bm1810/DataLogger/SCRIPTS/Temperature Sensors/Temperature_Sensors/DigiTempResponse/DigiTempResponse.ino

/*
  Temperature Sensors
 This code will read the temperature from two temperature sensors:
   Dallas 18820
   TMP36
 */

#include <OneWire.h>
#include <DallasTemperature.h>

// Data wire is plugged into pin 3 on the Arduino
#define ONE_WIRE_BUS 3

// Setup a oneWire instance to communicate with any OneWire devices
OneWire oneWire(ONE_WIRE_BUS);

// Pass our oneWire reference to Dallas Temperature. 
DallasTemperature sensors(&oneWire);

// Insert digital thermometer device IDs
DeviceAddress digiThermometer = { 0x28, 0xFF, 0xAC, 0x2C, 0x4E, 0x04, 0x00, 0xC6 };

// the setup routine runs once when you press reset:
void setup(void) {
  // initialize serial communication at 9600 bits per second:
  Serial.begin(115200);
  //start the sensors library
  sensors.begin();
  // set the resolution to 12 bit
  sensors.setResolution(digiThermometer, 12);
}

//float digitalTemp(DeviceAddress deviceAddress)
//{
//  sensors.requestTemperatures();
//  // read the digital temperature sensor value
//  float dgtlTemp = sensors.getTempC(deviceAddress);
//  
//  // if there is -127, there is no value being read, hence:
//  if (dgtlTemp == -127.00) {
//    Serial.print("Error getting temperature");
//  }
//  // Delay to allow processing time
//  return dgtlTemp;
//}


void loop() {
  
  // -------- Digital temperature sensor -------- //
  
  //Print the Temperature data with a timestamp from the chip (not RTC)
  sensors.requestTemperatures();
  Serial.println(micros());
  Serial.println(sensors.getTempC(digiThermometer));
}
